LibrEduc/CIM1-Projet-Simon/Photos/Vue sans le pcb.jpg

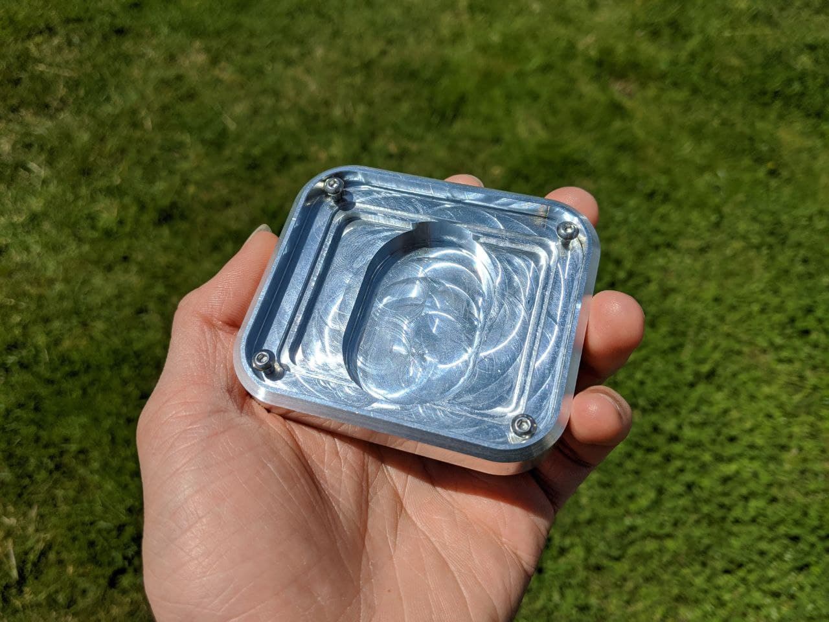
Photos/Vue sans le pcb.jpg
