LibrEduc/CIM1-Projet-Simon/Software/Programmes d'essais sur TinkerCad/Capture1TinkercadProgramme3.4.png

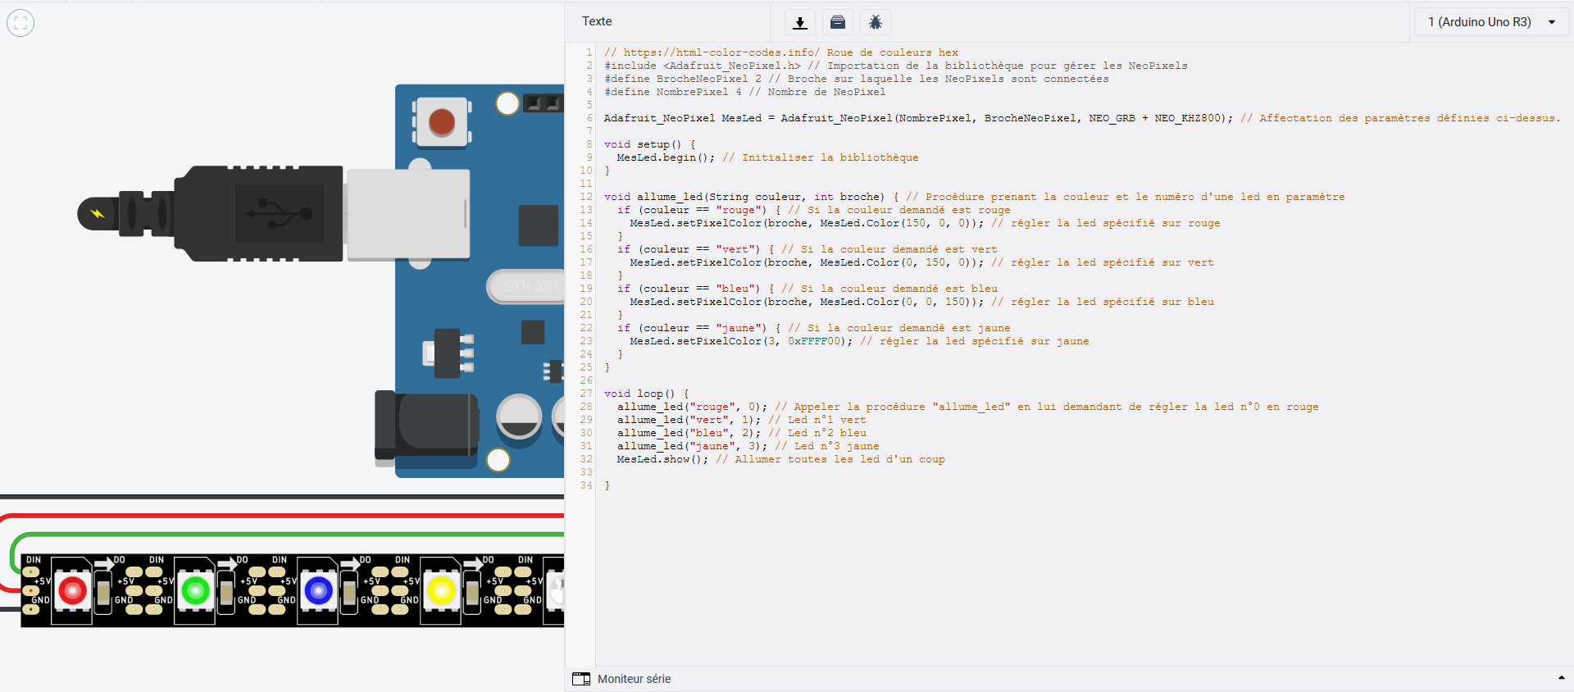
Software/Programmes d'essais sur TinkerCad/Capture1TinkercadProgramme3.4.png
