LibrEduc/CIM1-Projet-Simon/Software/Programmes d'essais sur TinkerCad/Capture2TinkercadProgramme5.png

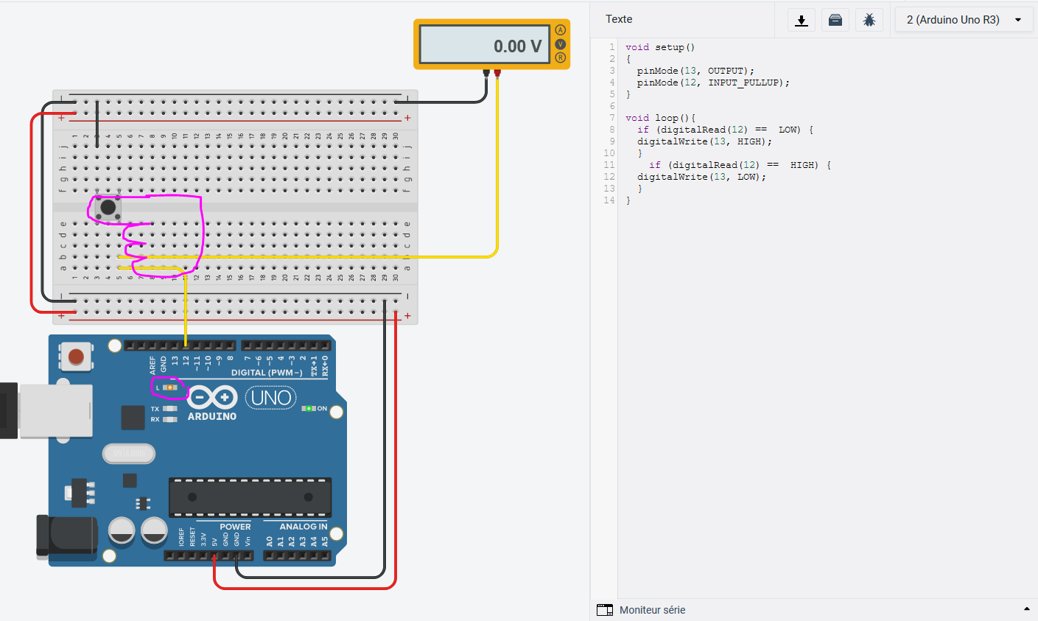
Software/Programmes d'essais sur TinkerCad/Capture2TinkercadProgramme5.png
